Jstn1321/C.H.A.S.E.R/Photoshoot/ChuaSignal.png

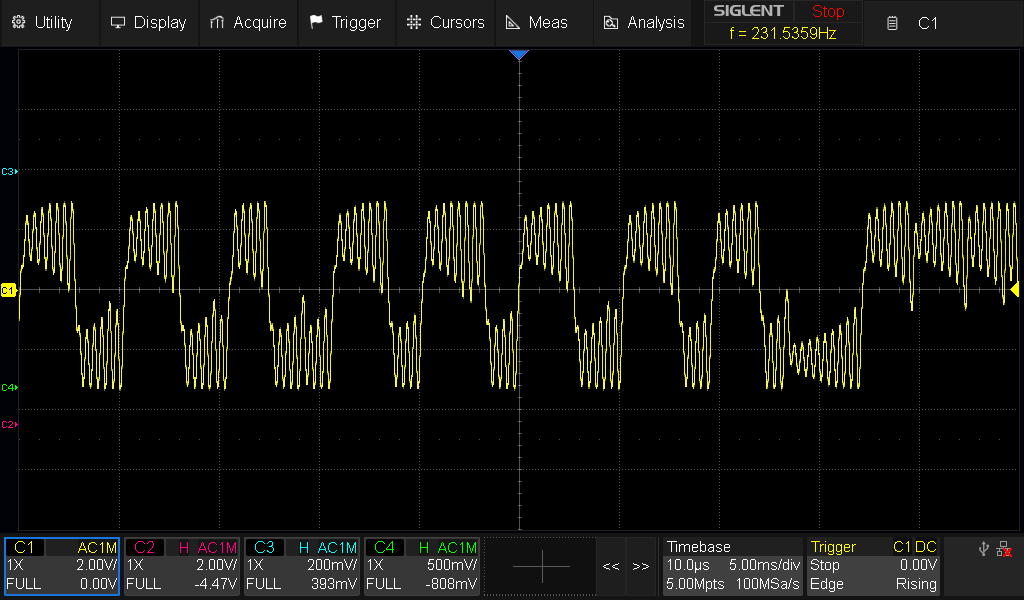
Photoshoot/ChuaSignal.png
