Jstn1321/C.H.A.S.E.R/Photoshoot/Data/Graphs/Modulation-Circuit/FFTs/SDS824X_HD_PNG_34.png

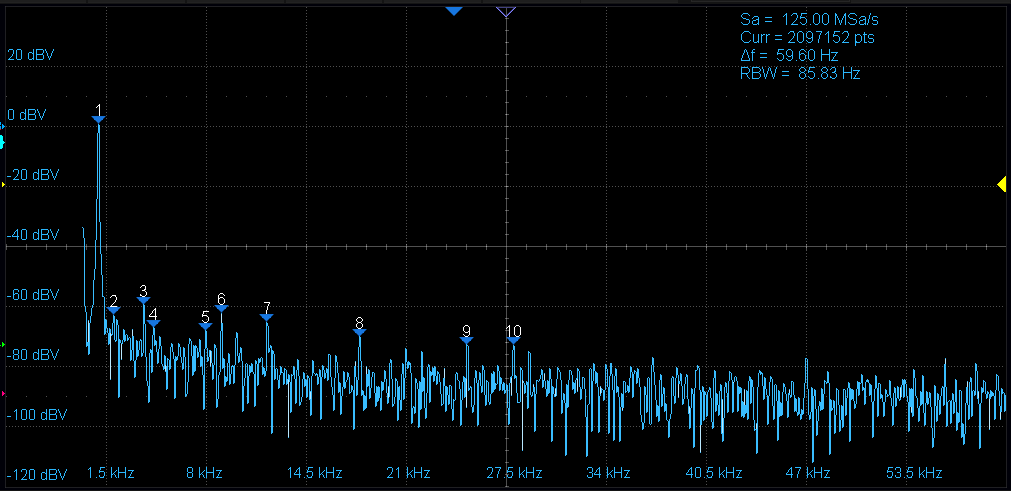
Photoshoot/Data/Graphs/Modulation-Circuit/FFTs/SDS824X_HD_PNG_34.png
