Jstn1321/C.H.A.S.E.R/Photoshoot/Data/Graphs/Modulation-Circuit/MATLAB/All_Graphs_Combined.png

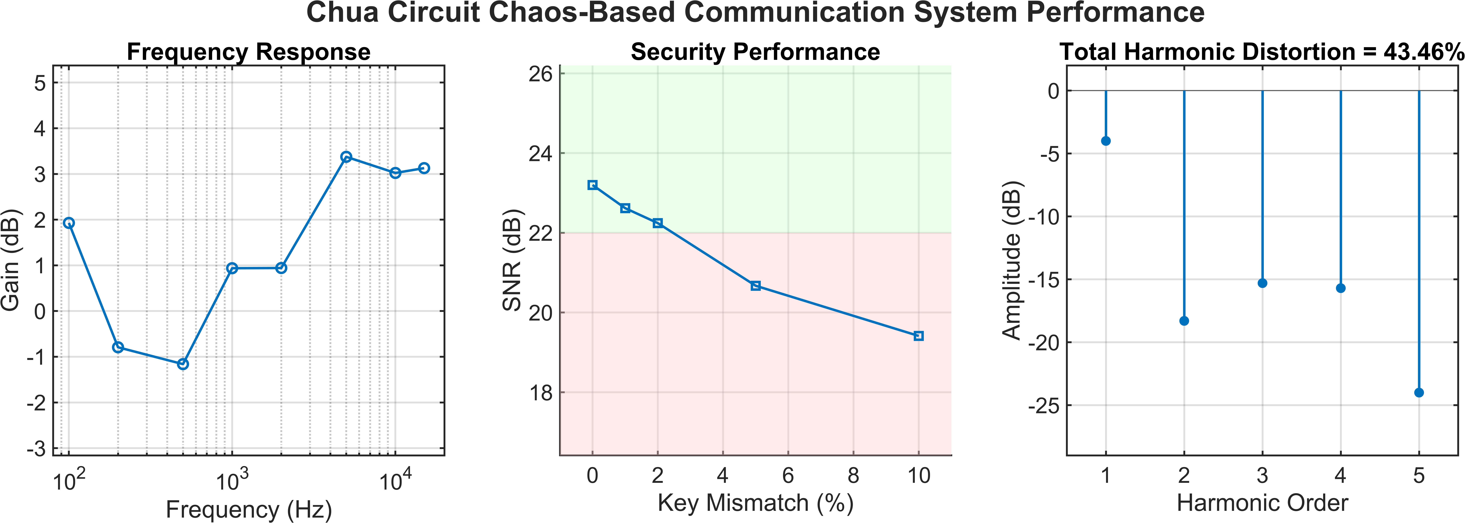
Photoshoot/Data/Graphs/Modulation-Circuit/MATLAB/All_Graphs_Combined.png
