Jstn1321/C.H.A.S.E.R/Photoshoot/Data/Graphs/Modulation-Circuit/MATLAB/Frequency_Response.png

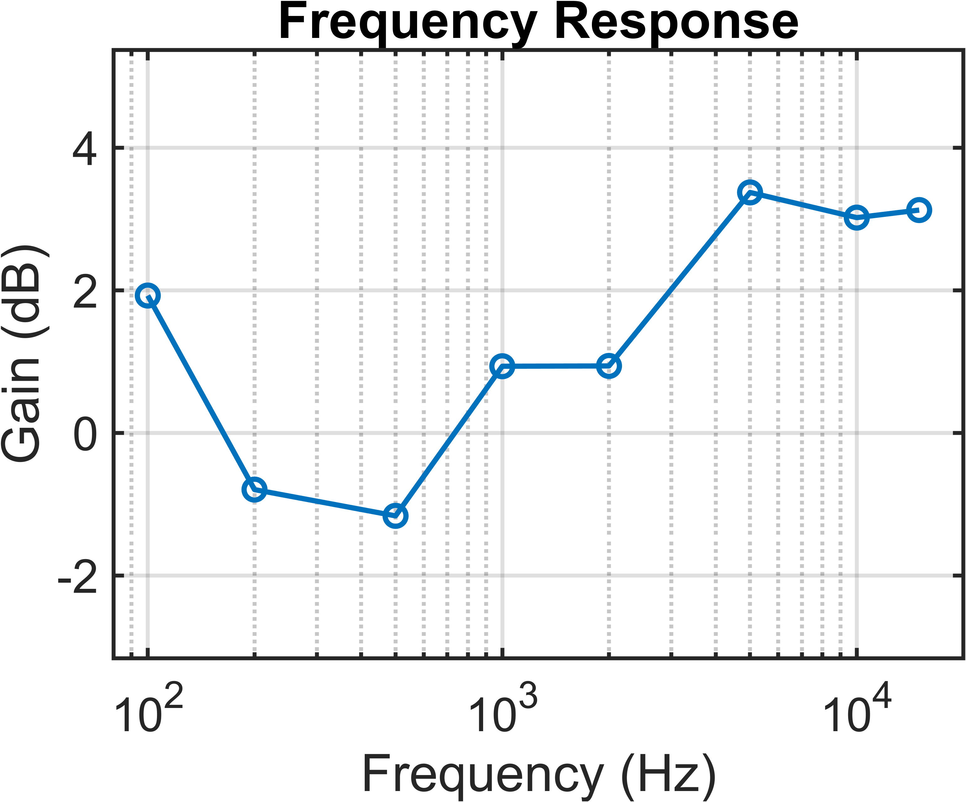
Photoshoot/Data/Graphs/Modulation-Circuit/MATLAB/Frequency_Response.png
