Jstn1321/C.H.A.S.E.R/Photoshoot/Data/Graphs/Modulation-Circuit/MATLAB/THD_Analysis.png

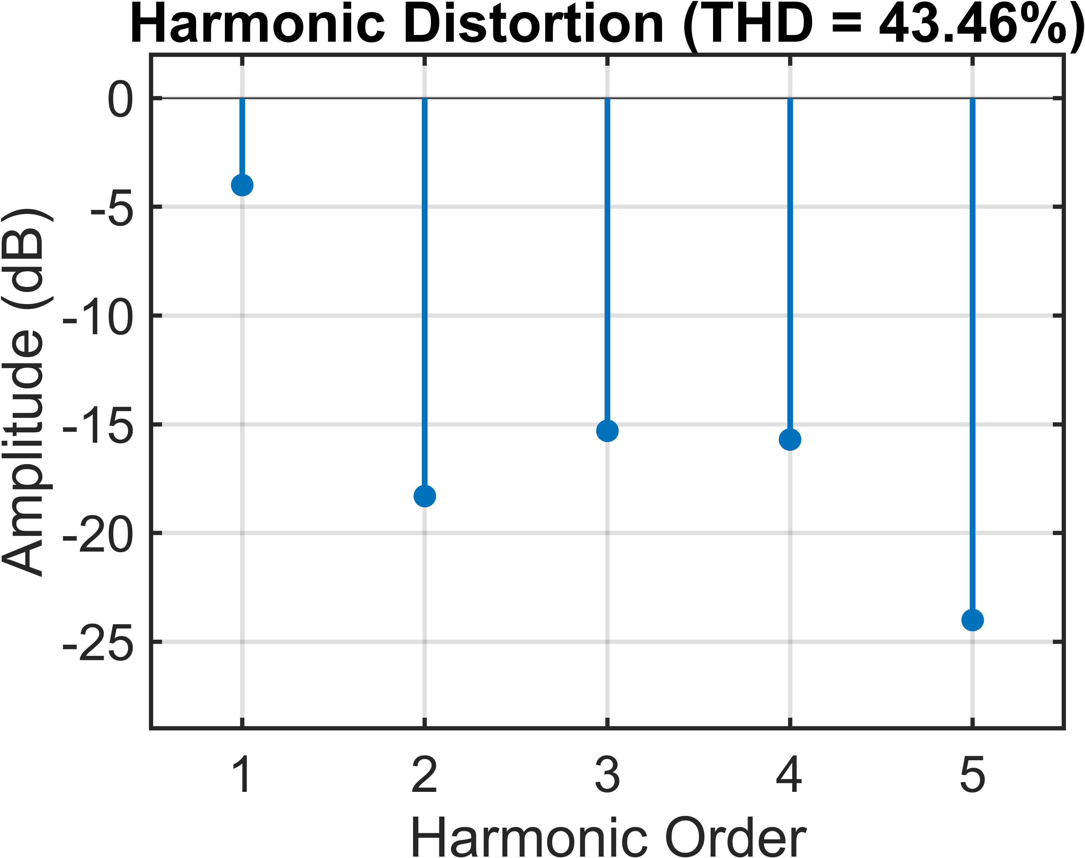
Photoshoot/Data/Graphs/Modulation-Circuit/MATLAB/THD_Analysis.png
