Jstn1321/C.H.A.S.E.R/Photoshoot/Data/Graphs/Modulation-Circuit/Time-Domain/SDS824X_HD_PNG_39.png

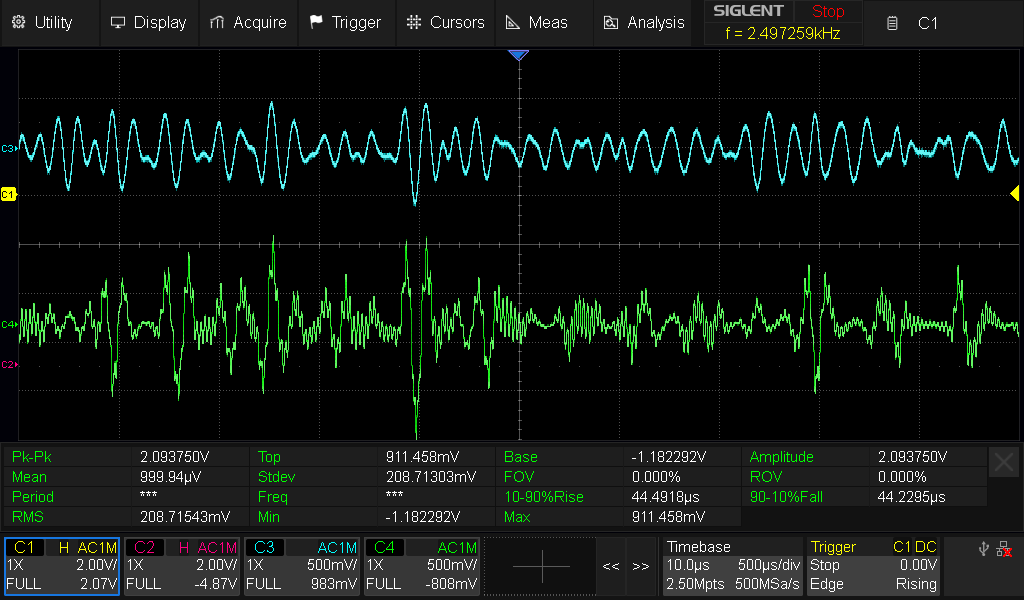
Photoshoot/Data/Graphs/Modulation-Circuit/Time-Domain/SDS824X_HD_PNG_39.png
