Jstn1321/C.H.A.S.E.R/Photoshoot/Data/Graphs/Summing-Circuit/Double-Scroll/Double-Scroll.png

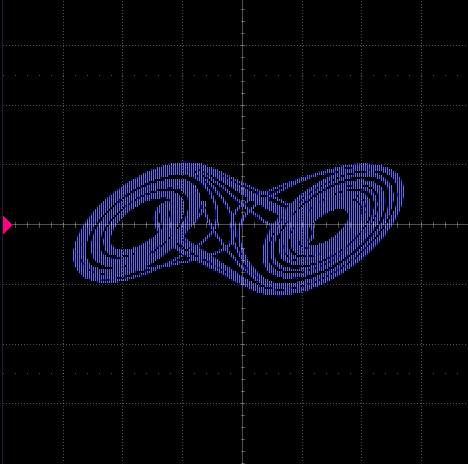
Photoshoot/Data/Graphs/Summing-Circuit/Double-Scroll/Double-Scroll.png
