Jstn1321/C.H.A.S.E.R/Photoshoot/Data/Graphs/Summing-Circuit/FFTs/Chua+Audio1.png

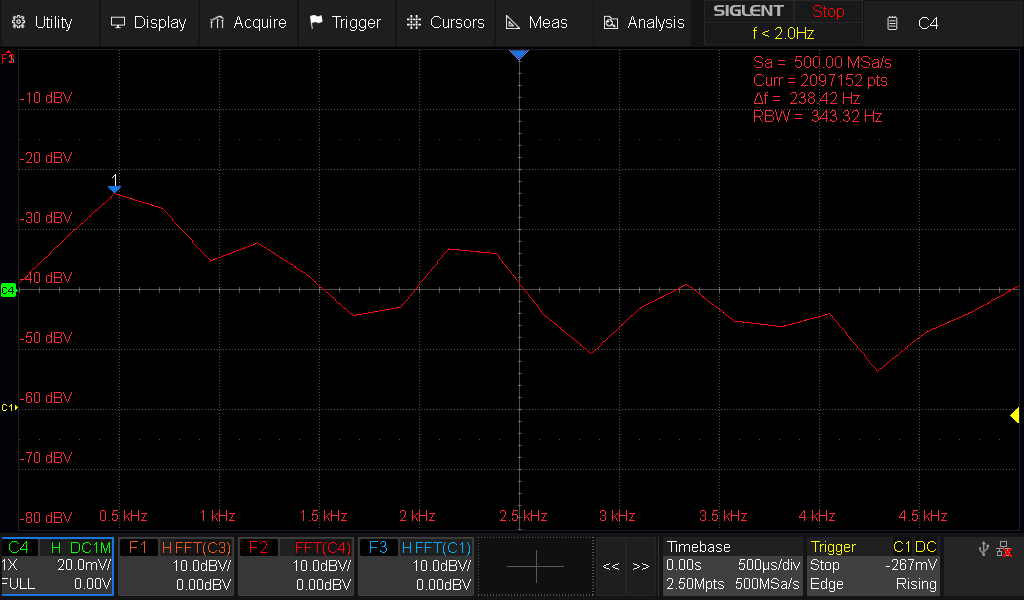
Photoshoot/Data/Graphs/Summing-Circuit/FFTs/Chua+Audio1.png
