Jstn1321/C.H.A.S.E.R/Photoshoot/Data/Graphs/Summing-Circuit/FFTs/RawAudio.png

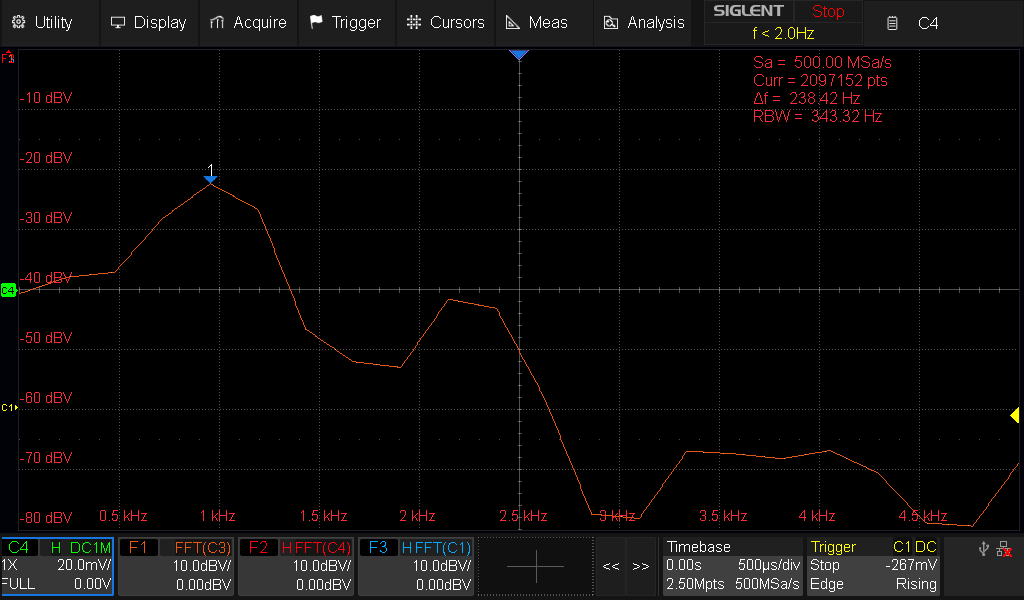
Photoshoot/Data/Graphs/Summing-Circuit/FFTs/RawAudio.png
