Jstn1321/C.H.A.S.E.R/Photoshoot/Data/Graphs/Summing-Circuit/Param-Hopping/HIGH_SIGNAL.png

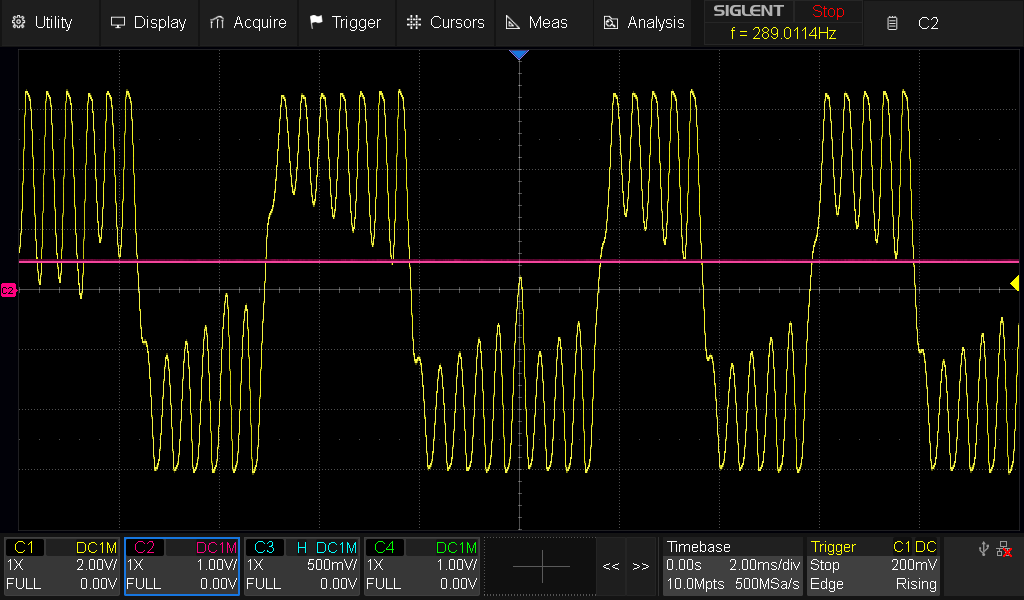
Photoshoot/Data/Graphs/Summing-Circuit/Param-Hopping/HIGH_SIGNAL.png
