Jstn1321/C.H.A.S.E.R/Photoshoot/Data/Graphs/Summing-Circuit/Param-Hopping/LOW_Signal.png

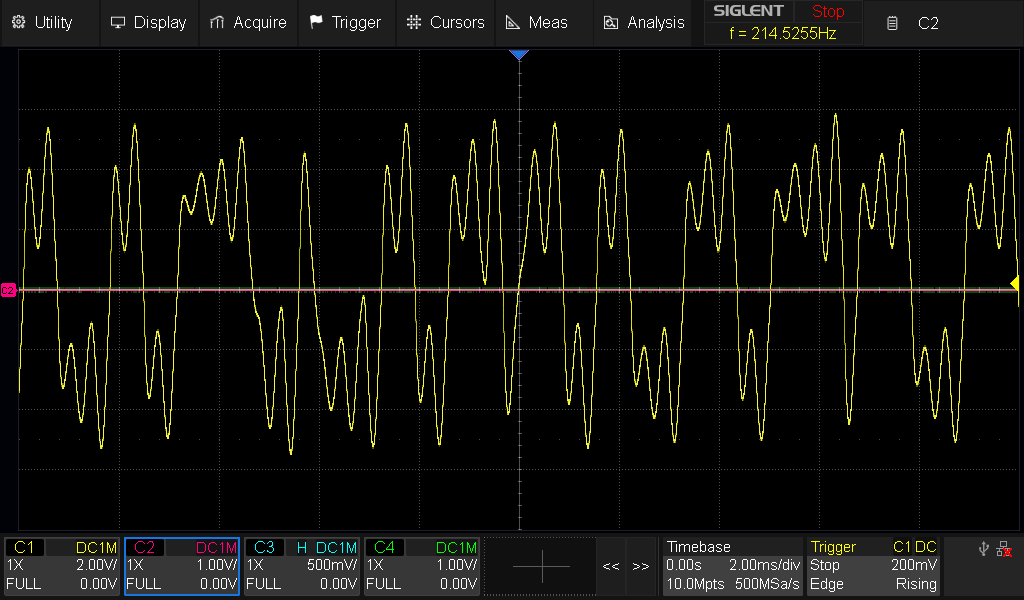
Photoshoot/Data/Graphs/Summing-Circuit/Param-Hopping/LOW_Signal.png
