Jstn1321/C.H.A.S.E.R/Photoshoot/Data/Graphs/Summing-Circuit/Time-Domain/Chaotic2.png

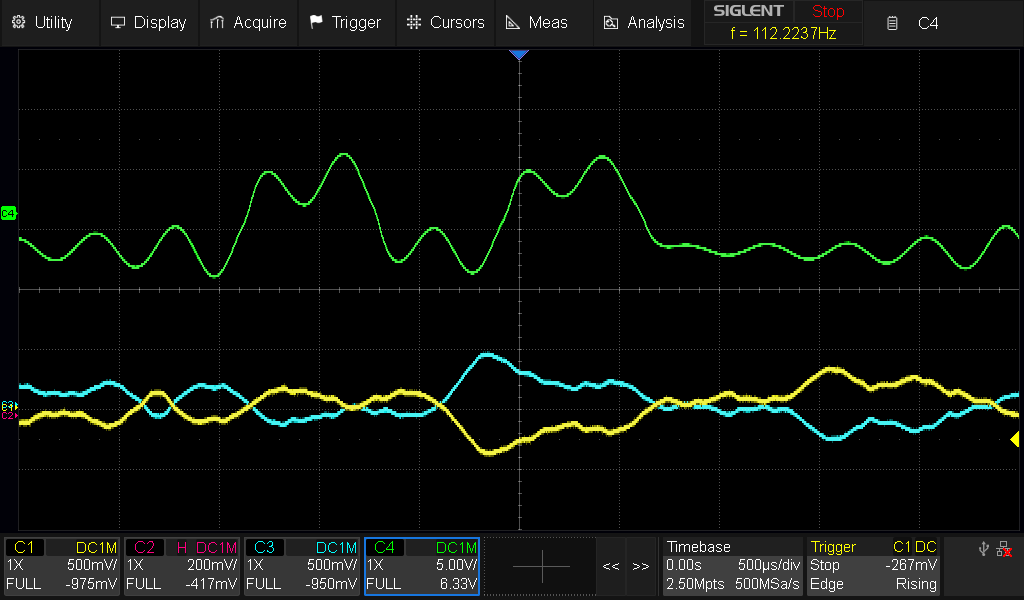
Photoshoot/Data/Graphs/Summing-Circuit/Time-Domain/Chaotic2.png
