Jstn1321/C.H.A.S.E.R/Photoshoot/Data/Graphs/Summing-Circuit/Time-Domain/ChaoticSin.png

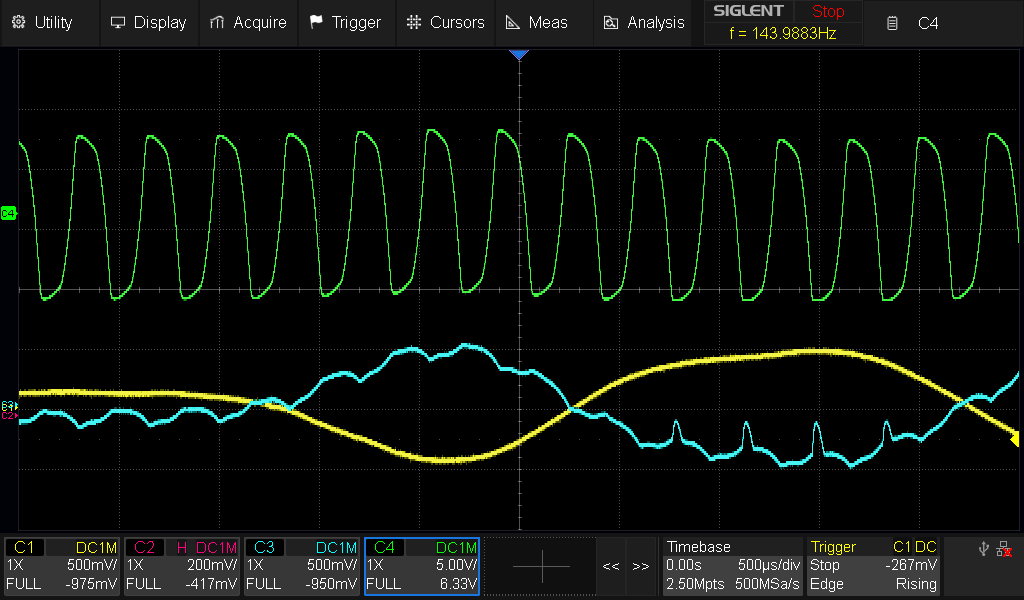
Photoshoot/Data/Graphs/Summing-Circuit/Time-Domain/ChaoticSin.png
