Jstn1321/C.H.A.S.E.R/Simulations/MATLAB/RealisticChuaSim/MATLABChuaSim.png

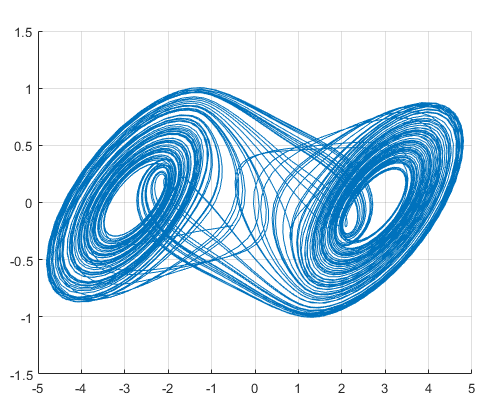
Simulations/MATLAB/RealisticChuaSim/MATLABChuaSim.png
