Jstn1321/C.H.A.S.E.R/Photoshoot/Data/Graphs/Modulation-Circuit/MATLAB/Security_Test.png

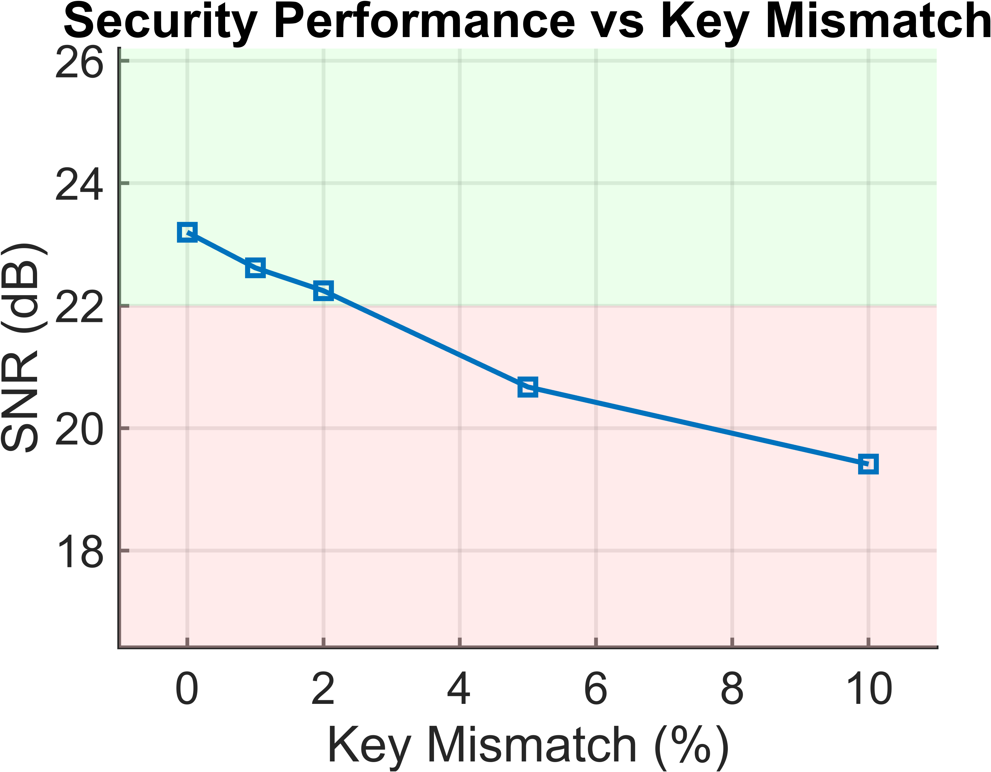
Photoshoot/Data/Graphs/Modulation-Circuit/MATLAB/Security_Test.png
